yuanyong2024/pico-wm/pictures/1.jpg

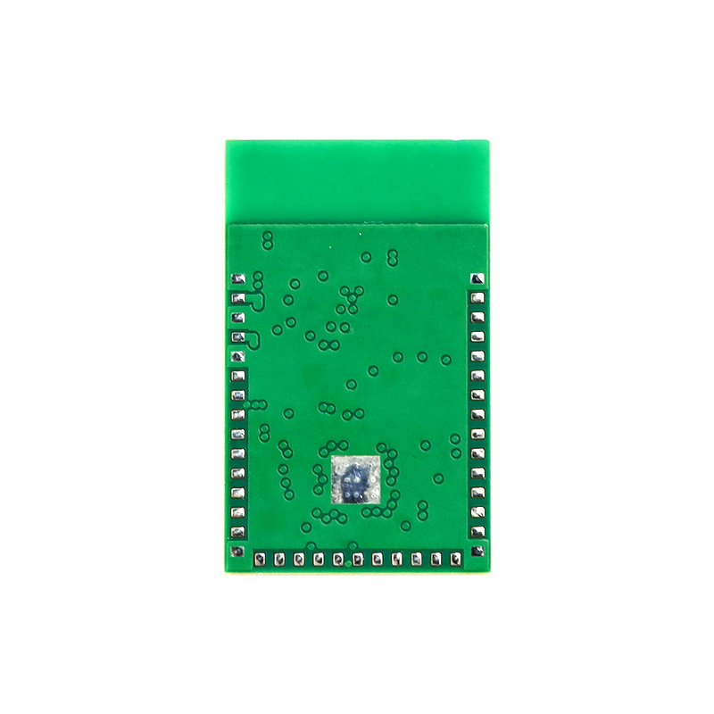
pictures/1.jpg
